hulonoj/TickerPCB/Firmware/include/stateMachine.h

#ifndef STATE_MACHINE_H
#define STATE_MACHINE_H

#include <Arduino.h>

void state_machine();

void state_machine();

void stock_selector();

void chess_selector();

void chessTickTick();

char alph_index(int &pos);

String ticker_to_string();

void STATE_Stock();
void STATE_Temperature();


#endif
